SamFOwens/D.I.Wireless/LTSpice/EmagsProj.asc

C1: cap; 0.47µ
D1: schottky; 1N5817
D2: schottky; 1N5817
D3: schottky; 1N5817
D4: schottky; 1N5817
D5: schottky; 1N5817
D6: schottky; 1N5817
D7: schottky; 1N5817
D8: schottky; 1N5817
L1: ind2; 1.24
L2: ind2; 330m
L3: ind2; 330m
L4: ind2; 1.24
L5: ind2; 330m
L6: ind2; 330m
L7: ind2; 10µ
L8: ind2; 26µ
L9: ind2; 1.24
L10: ind2; 330m
L11: ind2; 330m
L12: ind2; 1.24
L13: ind2; 330m
L14: ind2; 330m
R1: res; 25
R2: res; 50
R3: res; 0.001
R4: res; 25
R5: res; 0.001
R6: res; 11
R7: res; 50
U1: opamp2; LM324
V1: voltage; SINE(0 0.5 500)
V2: voltage; SINE(0 3 100k 2u)
V3: voltage; 5
V4: voltage; SINE(0 3 100k 1u)
V5: voltage; -5
Named nets: 0, VO1, Vin, Vc, VO2, Vin2, Vcc, Vnn
K1 L1 L2 L3 1
K2 L4 L5 L6 1
.tran 10m
K3 L7 L8 1
K4 L9 L10 L11 1
K5 L12 L13 L14 1
4
5
6
1
3
1
2
3
4
6
1
3
4
5
6
1
2
3
4
6
.include LM324.sub
