SamFOwens/D.I.Wireless/KiCad/DI Wireless Schematic/DI Wireless Schematic.kicad_sch

## KiCad design KiCad/DI Wireless Schematic/DI Wireless Schematic.kicad_sch (2026-05-07, an earlier design)

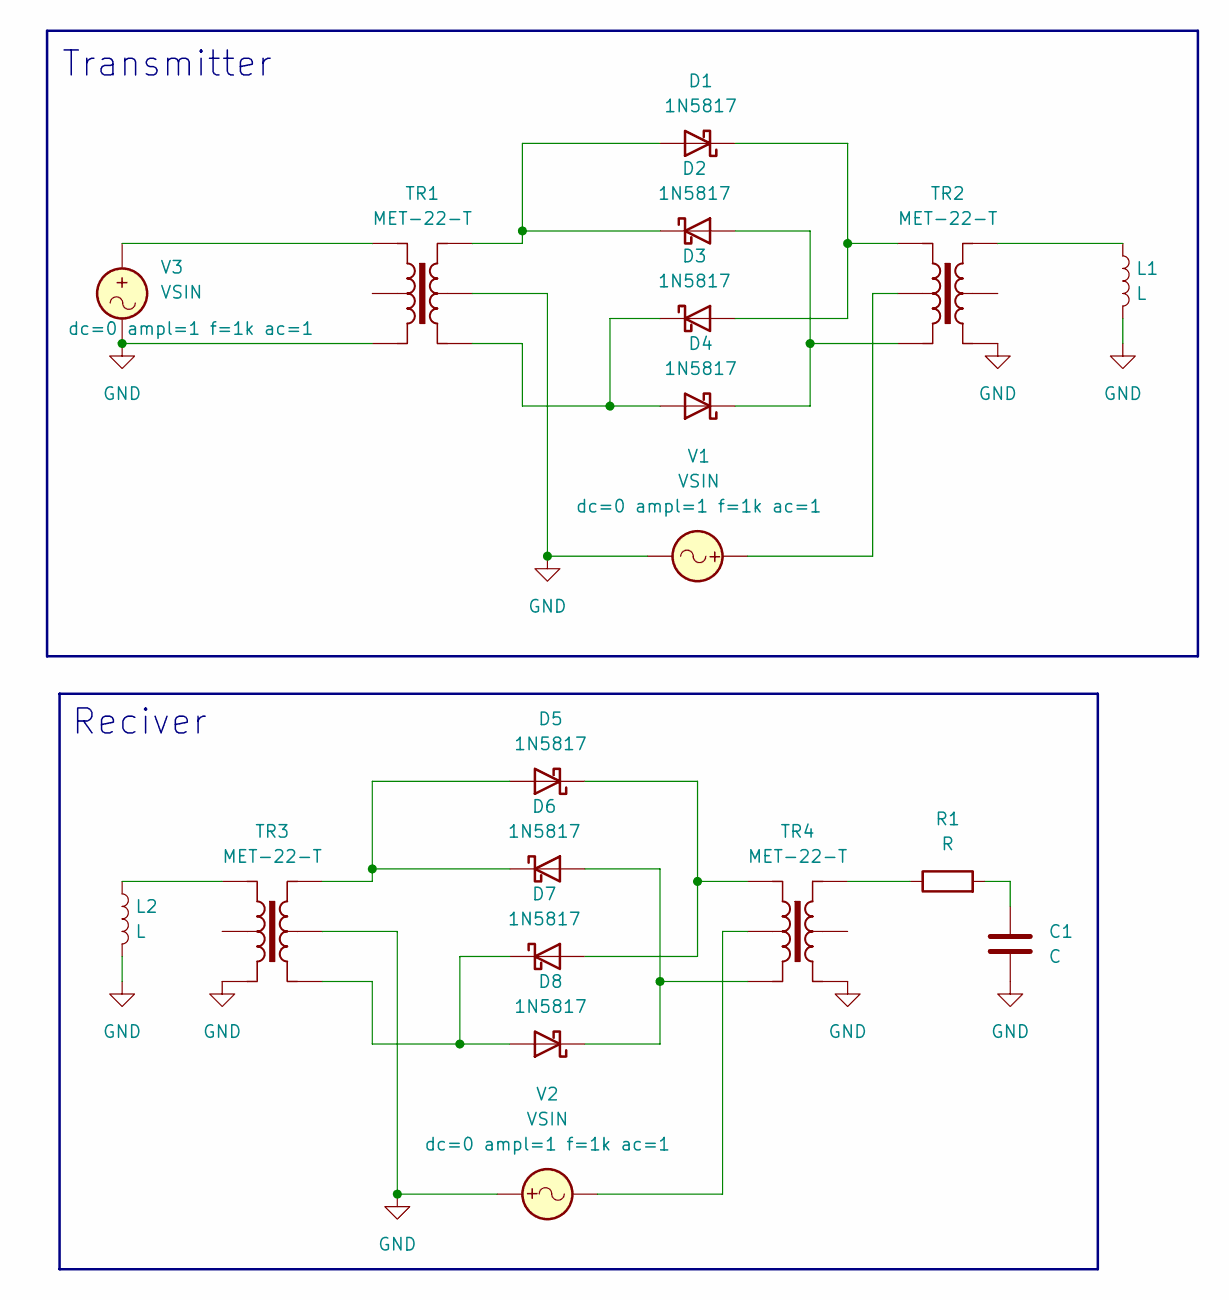
[picture p7: schematic DI Wireless Schematic.kicad_sch]

Parts:
C1: C
D1, D2, D3, D4, D5, D6, D7, D8: 1N5817; D_DO-41_SOD81_P10.16mm_Horizontal
L1, L2: L
R1: R
TR1, TR2, TR3, TR4: MET-22-T
V1, V2, V3: VSIN

Connections:
GND: C1.2, L1.2, L2.2, TR1.3, TR1.5, TR2.4, TR3.3, TR3.5, TR4.4, V1.2, V2.1, V3.2
unnamed: C1.1, R1.2
unnamed: D1.1 (K), D3.2 (A), TR2.1
unnamed: D1.2 (A), D2.1 (K), TR1.6
unnamed: D2.2 (A), D4.1 (K), TR2.3
unnamed: D3.1 (K), D4.2 (A), TR1.4
unnamed: D5.1 (K), D7.2 (A), TR4.1
unnamed: D5.2 (A), D6.1 (K), TR3.6
unnamed: D6.2 (A), D8.1 (K), TR4.3
unnamed: D7.1 (K), D8.2 (A), TR3.4
unnamed: L1.1, TR2.6
unnamed: L2.1, TR3.1
unnamed: R1.1, TR4.6
unnamed: TR1.1, V3.1
unnamed: TR2.2, V1.1
unnamed: TR4.2, V2.2

Notes on the sheet:
Reciver
Transmitter
